alegoldstein/Webcam/Photos/home.png

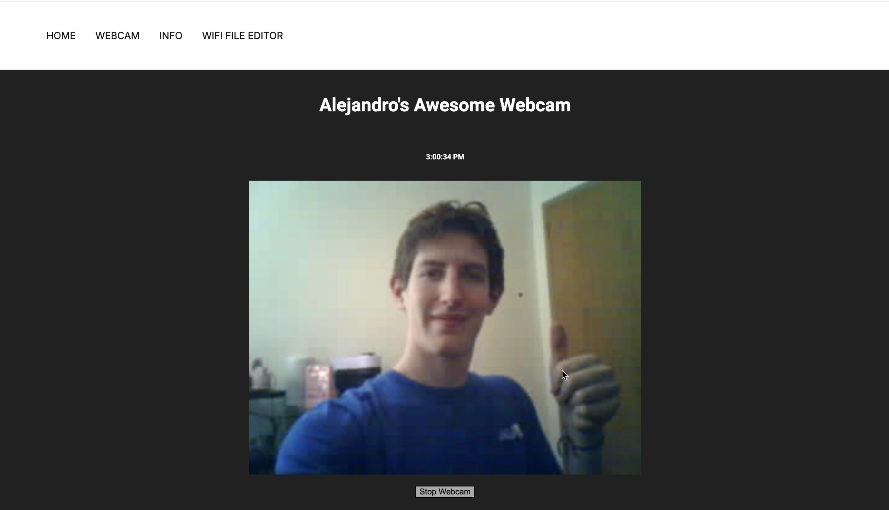
Photos/home.png
