alegoldstein/Webcam/EE326 Firmware/wifi.c

/*
 * wifi.c
 *
 * Created: 1/31/2023 1:02:43 PM
 *  Author: imikh
 */ 

#include <asf.h>
#include "wifi.h"

volatile uint32_t transfer_index = 0;
volatile uint32_t transfer_len = 0;

void SPI_Handler(void)
{
	uint32_t new_cmd = 0;
	static uint16_t data;
	uint8_t uc_pcs;

	if (spi_read_status(SPI) & SPI_SR_RDRF) {
		spi_read(SPI, &data, &uc_pcs);
		
		if (transfer_len--) {
			spi_write(SPI, transfer_index++, 0, 0);
		}
	}
}

void configure_usart_wifi(void)
{
	gpio_configure_pin(PIN_USART0_RXD_IDX, PIN_USART0_RXD_FLAGS);
	gpio_configure_pin(PIN_USART0_TXD_IDX, PIN_USART0_TXD_FLAGS);
	
	static uint32_t ul_sysclk;
	const sam_usart_opt_t wifi_usart_settings = {
		WIFI_USART_BAUDRATE,
		WIFI_USART_CHAR_LENGTH,
		WIFI_USART_PARITY,
		WIFI_USART_STOP_BITS,
		WIFI_USART_MODE,
		/* This field is only used in IrDA mode. */
		0
	};
	
	/* Get system clock. */
	ul_sysclk = sysclk_get_cpu_hz();
	
	pmc_enable_periph_clk(WIFI_USART_ID);
	
	usart_init_rs232(WIFI_USART,&wifi_usart_settings,ul_sysclk);

	/* Disable all the interrupts. */
	usart_disable_interrupt(WIFI_USART, ALL_INTERRUPT_MASK);
	
	/* Enable TX & RX function. */
	usart_enable_tx(WIFI_USART);
	usart_enable_rx(WIFI_USART);

	usart_enable_interrupt(WIFI_USART, US_IER_RXRDY);

	/* Configure and enable interrupt of USART. */
	NVIC_EnableIRQ(WIFI_USART_IRQn);
}

void configure_spi()
{
	gpio_configure_pin(SPI_MISO_GPIO, SPI_MISO_FLAGS);
	gpio_configure_pin(SPI_MOSI_GPIO, SPI_MOSI_FLAGS);
	gpio_configure_pin(SPI_SPCK_GPIO, SPI_SPCK_FLAGS);
	gpio_configure_pin(SPI_NPCS0_GPIO, SPI_NPCS0_FLAGS);
	
	/* Configure SPI interrupts for slave only. */
	NVIC_DisableIRQ(SPI_IRQn);
	NVIC_ClearPendingIRQ(SPI_IRQn);
	NVIC_SetPriority(SPI_IRQn, 0);
	NVIC_EnableIRQ(SPI_IRQn);
}

void spi_peripheral_initialize(void)
{
	spi_enable_clock(SPI);
	spi_disable(SPI);
	spi_reset(SPI);
	spi_set_slave_mode(SPI);
	spi_disable_mode_fault_detect(SPI);
	spi_set_peripheral_chip_select_value(SPI, SPI_CHIP_PCS);
	spi_set_clock_polarity(SPI, SPI_CHIP_SEL, SPI_CLK_POLARITY);
	spi_set_clock_phase(SPI, SPI_CHIP_SEL, SPI_CLK_PHASE);
	spi_set_bits_per_transfer(SPI, SPI_CHIP_SEL, SPI_CSR_BITS_8_BIT);
	spi_enable_interrupt(SPI, SPI_IER_RDRF);
	spi_enable(SPI);
}

void spi_prep_transfer(void)
{
	transfer_len = 100;
	transfer_index = 0;
}
