alegoldstein/Webcam/EE326 Firmware/ov7740_example.c

/**
 * \file
 *
 * \brief OV7740 image sensor capture example.
 *
 * Copyright (c) 2014-2018 Microchip Technology Inc. and its subsidiaries.
 *
 * \asf_license_start
 *
 * \page License
 *
 * Subject to your compliance with these terms, you may use Microchip
 * software and any derivatives exclusively with Microchip products.
 * It is your responsibility to comply with third party license terms applicable
 * to your use of third party software (including open source software) that
 * may accompany Microchip software.
 *
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
 * \asf_license_stop
 *
 */

/**
 * \mainpage OV7740 image sensor capture example.
 *
 * \section Purpose
 *
 * This example demonstrates how to configure the OV7740 to capture a picture
 * and display it on LCD.
 *
 * \section Requirements
 *
 * This package can be used with sam4s_wpir_rd board.
 *
 * \section Description
 *
 * This example first sets the PLLB to the system core clock and PLLA to clock
 * PCK0 (used to get data from image sensor). Next step is to configure the
 * LCD controller and display information to the user. Then external SRAM, which
 * is used to store data after acquisition, is configured. Finally this example
 * configures the OV7740 CMOS image sensor and the PIO capture.
 * When the user presses the push button, a picture is captured, stored
 * to the external SRAM memory and finally displayed on the LCD.
 *
 * \section Usage
 *
 * -# Build the program and download it inside the evaluation board.
 *
 */
/*
 * Support and FAQ: visit <a href="https://www.microchip.com/support/">Microchip Support</a>
 */

#include "asf.h"
#include "conf_board.h"
#include "conf_clock.h"

/* Uncomment this macro to work in black and white mode */
#define DEFAULT_MODE_COLORED

#ifndef PIO_PCMR_DSIZE_WORD
#  define PIO_PCMR_DSIZE_WORD PIO_PCMR_DSIZE(2)
#endif

/* TWI clock frequency in Hz (400KHz) */
#define TWI_CLK     (400000UL)

/* Pointer to the image data destination buffer */
uint8_t *//camera pin, variable, and function declarations
//camera TWI parameters



#ifndef camera_h
#define camera_h

#include "asf.h"
#include <stdint.h>
#include <stdio.h>
#include "pio.h"
//#include <twi_master.h>
#include <pmc.h>
#include <gpio.h>
#include <sysclk.h>
#include "ov2640.h"

extern volatile uint32_t image_len;

#define OV2640_DATA_BUS_PIO     PIOA
#define OV2640_DATA_BUS_ID      ID_PIOA
#define PIN_VSYNC_PIO           PIOA
#define OV2640_VSYNC_ID         ID_PIOA
#define OV2640_VSYNC_MASK       (1 << 15)
#define OV2640_VSYNC_TYPE       PIO_IT_RISE_EDGE
#define BOARD_TWI				TWI0

#define CAP_BUFFER_SIZE     (100000)         // 20KB, safe upper bound for JPEG 320x240
extern uint8_t g_p_uc_cap_dest_buf[];

//handler for rising edge of vsync, set flag
void vsync_handler(uint32_t ul_id, uint32_t ul_mask);

//configure vsync interrupt
void init_vsync_interrupts(void);

//configure TWI (two wire interface I2C)
void configure_twi(void);

//configure and initialize parallel capture 
void pio_capture_init(Pio *p_pio, uint32_t ul_id);

//use parallel capture and PDC to store images in buffer
uint8_t pio_capture_to_buffer(Pio *p_pio, uint8_t *uc_buf, uint32_t ul_size);

//configure camera pins and clk (XCLK), and call configure_twi()
void init_camera(void);

//configure camera registers
void configure_camera(void);

//capture image on rising edge of vsync, gets image length and returns 1 on success and 0 on fail
uint8_t start_capture(void);

//finds image length based on JPED protocol, can find start of image (SOI) before end of image (EOI)
//return 1 if success 0 and 0 if failure
uint8_t find_image_len(void);

#endif;

/* Rows size of capturing picture */
uint16_t g_us_cap_rows = IMAGE_HEIGHT;

/* Define display function and line size of captured picture according to the */
/* current mode (color or black and white) */
#ifdef DEFAULT_MODE_COLORED
	#define _display() draw_frame_yuv_color_int()

	/* (IMAGE_WIDTH *2 ) because ov7740 use YUV422 format in color mode */
	/* (draw_frame_yuv_color_int for more details) */
	uint16_t g_us_cap_line = (IMAGE_WIDTH * 2);
#else
	#define _display() draw_frame_yuv_bw8()

	uint16_t g_us_cap_line = (IMAGE_WIDTH);
#endif

/* Push button information (true if it's triggered and false otherwise) */
static volatile uint32_t g_ul_push_button_trigger = false;

/* Vsync signal information (true if it's triggered and false otherwise) */
static volatile uint32_t g_ul_vsync_flag = false;

/**
 * \brief Handler for vertical synchronisation using by the OV7740 image
 * sensor.
 */
static void vsync_handler(uint32_t ul_id, uint32_t ul_mask)
{
	unused(ul_id);
	unused(ul_mask);

	g_ul_vsync_flag = true;
}

/**
 * \brief Handler for button rising edge interrupt.
 */
static void button_handler(uint32_t ul_id, uint32_t ul_mask)
{
	unused(ul_id);
	unused(ul_mask);

	g_ul_push_button_trigger = true;
}

/**
 * \brief Intialize Vsync_Handler.
 */
static void init_vsync_interrupts(void)
{
	/* Initialize PIO interrupt handler, see PIO definition in conf_board.h
	**/
	pio_handler_set(OV7740_VSYNC_PIO, OV7740_VSYNC_ID, OV7740_VSYNC_MASK,
			OV7740_VSYNC_TYPE, vsync_handler);

	/* Enable PIO controller IRQs */
	NVIC_EnableIRQ((IRQn_Type)OV7740_VSYNC_ID);
}

/**
 * \brief Configure push button and initialize button_handler interrupt.
 */
static void configure_button(void)
{
	/* Configure PIO clock. */
	pmc_enable_periph_clk(PUSH_BUTTON_ID);

	/* Adjust PIO debounce filter using a 10 Hz filter. */
	pio_set_debounce_filter(PUSH_BUTTON_PIO, PUSH_BUTTON_PIN_MSK, 10);

	/* Initialize PIO interrupt handler, see PIO definition in conf_board.h
	**/
	pio_handler_set(PUSH_BUTTON_PIO, PUSH_BUTTON_ID, PUSH_BUTTON_PIN_MSK,
			PUSH_BUTTON_ATTR, button_handler);

	/* Enable PIO controller IRQs. */
	NVIC_EnableIRQ((IRQn_Type)PUSH_BUTTON_ID);

	/* Enable PIO interrupt lines. */
	pio_enable_interrupt(PUSH_BUTTON_PIO, PUSH_BUTTON_PIN_MSK);
}

/**
 * \brief Initialize PIO capture for the OV7740 image sensor communication.
 *
 * \param p_pio PIO instance to be configured in PIO capture mode.
 * \param ul_id Corresponding PIO ID.
 */
static void pio_capture_init(Pio *p_pio, uint32_t ul_id)
{
	/* Enable periphral clock */
	pmc_enable_periph_clk(ul_id);

	/* Disable pio capture */
	p_pio->PIO_PCMR &= ~((uint32_t)PIO_PCMR_PCEN);

	/* Disable rxbuff interrupt */
	p_pio->PIO_PCIDR |= PIO_PCIDR_RXBUFF;

	/* 32bit width*/
	p_pio->PIO_PCMR &= ~((uint32_t)PIO_PCMR_DSIZE_Msk);
	p_pio->PIO_PCMR |= PIO_PCMR_DSIZE_WORD;

	/* Only HSYNC and VSYNC enabled */
	p_pio->PIO_PCMR &= ~((uint32_t)PIO_PCMR_ALWYS);
	p_pio->PIO_PCMR &= ~((uint32_t)PIO_PCMR_HALFS);

#if !defined(DEFAULT_MODE_COLORED)
	/* Samples only data with even index */
	p_pio->PIO_PCMR |= PIO_PCMR_HALFS;
	p_pio->PIO_PCMR &= ~((uint32_t)PIO_PCMR_FRSTS);
#endif
}

/**
 * \brief Capture OV7740 data to a buffer.
 *
 * \param p_pio PIO instance which will capture data from OV7740 iamge sensor.
 * \param p_uc_buf Buffer address where captured data must be stored.
 * \param ul_size Data frame size.
 */
static uint8_t pio_capture_to_buffer(Pio *p_pio, uint8_t *uc_buf,
		uint32_t ul_size)
{
	/* Check if the first PDC bank is free */
	if ((p_pio->PIO_RCR == 0) && (p_pio->PIO_RNCR == 0)) {
		p_pio->PIO_RPR = (uint32_t)uc_buf;
		p_pio->PIO_RCR = ul_size;
		p_pio->PIO_PTCR = PIO_PTCR_RXTEN;
		return 1;
	} else if (p_pio->PIO_RNCR == 0) {
		p_pio->PIO_RNPR = (uint32_t)uc_buf;
		p_pio->PIO_RNCR = ul_size;
		return 1;
	} else {
		return 0;
	}
}

/**
 * \brief Intialize LCD display.
 */
static void display_init(void)
{
	struct ili9325_opt_t ili9325_display_opt;

	/* Enable peripheral clock */
	pmc_enable_periph_clk( ID_SMC );

	/* Configure SMC interface for LCD */
	smc_set_setup_timing(SMC, ILI9325_LCD_CS, SMC_SETUP_NWE_SETUP(2)
			| SMC_SETUP_NCS_WR_SETUP(2)
			| SMC_SETUP_NRD_SETUP(2)
			| SMC_SETUP_NCS_RD_SETUP(2));

	smc_set_pulse_timing(SMC, ILI9325_LCD_CS, SMC_PULSE_NWE_PULSE(4)
			| SMC_PULSE_NCS_WR_PULSE(4)
			| SMC_PULSE_NRD_PULSE(10)
			| SMC_PULSE_NCS_RD_PULSE(10));

	smc_set_cycle_timing(SMC, ILI9325_LCD_CS, SMC_CYCLE_NWE_CYCLE(10)
			| SMC_CYCLE_NRD_CYCLE(22));

	smc_set_mode(SMC, ILI9325_LCD_CS, SMC_MODE_READ_MODE
			| SMC_MODE_WRITE_MODE);

	/* Initialize display parameter */
	ili9325_display_opt.ul_width = ILI9325_LCD_WIDTH;
	ili9325_display_opt.ul_height = ILI9325_LCD_HEIGHT;
	ili9325_display_opt.foreground_color = COLOR_BLACK;
	ili9325_display_opt.background_color = COLOR_WHITE;

	/* Switch off backlight */
	aat31xx_disable_backlight();

	/* Initialize LCD */
	ili9325_init(&ili9325_display_opt);

	/* Set backlight level */
	aat31xx_set_backlight(AAT31XX_MAX_BACKLIGHT_LEVEL);

	/* Turn on LCD */
	ili9325_display_on();
}

/**
 * \brief Initialize PIO capture and the OV7740 image sensor.
 */
static void capture_init(void)
{
	twi_options_t opt;

	/* Init Vsync handler*/
	init_vsync_interrupts();

	/* Init PIO capture*/
	pio_capture_init(OV_DATA_BUS_PIO, OV_DATA_BUS_ID);

	/* Turn on ov7740 image sensor using power pin */
	ov_power(true, OV_POWER_PIO, OV_POWER_MASK);

	/* Init PCK0 to work at 24 Mhz */
	/* 96/4=24 Mhz */
	PMC->PMC_PCK[0] = (PMC_PCK_PRES_CLK_4 | PMC_PCK_CSS_PLLA_CLK);
	PMC->PMC_SCER = PMC_SCER_PCK0;
	while (!(PMC->PMC_SCSR & PMC_SCSR_PCK0)) {
	}

	/* Enable TWI peripheral */
	pmc_enable_periph_clk(ID_BOARD_TWI);

	/* Init TWI peripheral */
	opt.master_clk = sysclk_get_cpu_hz();
	opt.speed      = TWI_CLK;
	twi_master_init(BOARD_TWI, &opt);

	/* Configure TWI interrupts */
	NVIC_DisableIRQ(BOARD_TWI_IRQn);
	NVIC_ClearPendingIRQ(BOARD_TWI_IRQn);
	NVIC_SetPriority(BOARD_TWI_IRQn, 0);
	NVIC_EnableIRQ(BOARD_TWI_IRQn);

	/* ov7740 Initialization */
	while (ov_init(BOARD_TWI) == 1) {
	}

	/* ov7740 configuration */
	ov_configure(BOARD_TWI, QVGA_YUV422_20FPS);

	/* Wait 3 seconds to let the image sensor to adapt to environment */
	delay_ms(3000);
}

/**
 * \brief Start picture capture.
 */
static void start_capture(void)
{
	/* Set capturing destination address*/
	g_p_uc_cap_dest_buf = (uint8_t *)CAP_DEST;

	/* Set cap_rows value*/
	g_us_cap_rows = IMAGE_HEIGHT;

	/* Enable vsync interrupt*/
	pio_enable_interrupt(OV7740_VSYNC_PIO, OV7740_VSYNC_MASK);

	/* Capture acquisition will start on rising edge of Vsync signal.
	 * So wait g_vsync_flag = 1 before start process
	 */
	while (!g_ul_vsync_flag) {
	}

	/* Disable vsync interrupt*/
	pio_disable_interrupt(OV7740_VSYNC_PIO, OV7740_VSYNC_MASK);

	/* Enable pio capture*/
	pio_capture_enable(OV7740_DATA_BUS_PIO);

	/* Capture data and send it to external SRAM memory thanks to PDC
	 * feature */
	pio_capture_to_buffer(OV7740_DATA_BUS_PIO, g_p_uc_cap_dest_buf,
			(g_us_cap_line * g_us_cap_rows) >> 2);

	/* Wait end of capture*/
	while (!((OV7740_DATA_BUS_PIO->PIO_PCISR & PIO_PCIMR_RXBUFF) ==
			PIO_PCIMR_RXBUFF)) {
	}

	/* Disable pio capture*/
	pio_capture_disable(OV7740_DATA_BUS_PIO);

	/* Reset vsync flag*/
	g_ul_vsync_flag = false;
}

/**
 * \brief Configure SMC interface for SRAM.
 */
static void board_configure_sram( void )
{
	/* Enable peripheral clock */
	pmc_enable_periph_clk( ID_SMC );

	/* Configure SMC interface for SRAM */
	smc_set_setup_timing(SMC, SRAM_CS, SMC_SETUP_NWE_SETUP(2)
			| SMC_SETUP_NCS_WR_SETUP(0)
			| SMC_SETUP_NRD_SETUP(3)
			| SMC_SETUP_NCS_RD_SETUP(0));

	smc_set_pulse_timing(SMC, SRAM_CS, SMC_PULSE_NWE_PULSE(4)
			| SMC_PULSE_NCS_WR_PULSE(5)
			| SMC_PULSE_NRD_PULSE(4)
			| SMC_PULSE_NCS_RD_PULSE(6));

	smc_set_cycle_timing(SMC, SRAM_CS, SMC_CYCLE_NWE_CYCLE(6)
			| SMC_CYCLE_NRD_CYCLE(7));

	smc_set_mode(SMC, SRAM_CS, SMC_MODE_READ_MODE
			| SMC_MODE_WRITE_MODE);
}

#ifdef DEFAULT_MODE_COLORED

/**
 * \brief Take a 32 bit variable in parameters and returns a value between 0 and
 * 255.
 *
 * \param i Enter value .
 * \return i if 0<i<255, 0 if i<0 and 255 if i>255
 */
static inline uint8_t clip32_to_8( int32_t i )
{
	if (i > 255) {
		return 255;
	}

	if (i < 0) {
		return 0;
	}

	return (uint8_t)i;
}

/**
 * \brief Draw LCD in color with integral algorithm.
 */
static void draw_frame_yuv_color_int( void )
{
	uint32_t ul_cursor;
	int32_t l_y1;
	int32_t l_y2;
	int32_t l_v;
	int32_t l_u;
	int32_t l_blue;
	int32_t l_green;
	int32_t l_red;
	uint8_t *p_uc_data;

	p_uc_data = (uint8_t *)g_p_uc_cap_dest_buf;

	/* Configure LCD to draw captured picture */
	LCD_IR(0);
	LCD_IR(ILI9325_ENTRY_MODE);
	LCD_WD(((ILI9325_ENTRY_MODE_BGR | ILI9325_ENTRY_MODE_AM |
			ILI9325_ENTRY_MODE_DFM | ILI9325_ENTRY_MODE_TRI |
			ILI9325_ENTRY_MODE_ORG) >> 8) & 0xFF);
	LCD_WD((ILI9325_ENTRY_MODE_BGR | ILI9325_ENTRY_MODE_AM |
			ILI9325_ENTRY_MODE_DFM | ILI9325_ENTRY_MODE_TRI |
			ILI9325_ENTRY_MODE_ORG) & 0xFF);
	ili9325_draw_prepare(0, 0, IMAGE_HEIGHT, IMAGE_WIDTH);

	/* OV7740 Color format is YUV422. In this format pixel has 4 bytes
	 * length (Y1,U,Y2,V).
	 * To display it on LCD,these pixel need to be converted in RGB format.
	 * The output of this conversion is two 3 bytes pixels in (B,G,R)
	 * format. First one is calculed using Y1,U,V and the other one with
	 * Y2,U,V. For that reason cap_line is twice bigger in color mode
	 * than in black and white mode. */
	for (ul_cursor = IMAGE_WIDTH * IMAGE_HEIGHT; ul_cursor != 0;
			ul_cursor -= 2, p_uc_data += 4) {
		l_y1 = p_uc_data[0]; /* Y1 */
		l_y1 -= 16;
		l_v = p_uc_data[3]; /* V */
		l_v -= 128;
		l_u = p_uc_data[1]; /* U */
		l_u -= 128;

		l_blue = 516 * l_v + 128;
		l_green = -100 * l_v - 208 * l_u + 128;
		l_red = 409 * l_u + 128;

		/* BLUE */
		LCD_WD( clip32_to_8((298 * l_y1 + l_blue) >> 8));
		/* GREEN */
		LCD_WD( clip32_to_8((298 * l_y1 + l_green) >> 8));
		/* RED */
		LCD_WD( clip32_to_8((298 * l_y1 + l_red) >> 8));

		l_y2 = p_uc_data[2]; /* Y2 */
		l_y2 -= 16;
		LCD_WD( clip32_to_8((298 * l_y2 + l_blue) >> 8));
		LCD_WD( clip32_to_8((298 * l_y2 + l_green) >> 8));
		LCD_WD( clip32_to_8((298 * l_y2 + l_red) >> 8));
	}
}

#else

/**
 * \brief Draw LCD in black and white with integral algorithm.
 */
static void draw_frame_yuv_bw8( void )
{
	volatile uint32_t ul_cursor;
	uint8_t *p_uc_data;

	p_uc_data = (uint8_t *)g_p_uc_cap_dest_buf;

	/* Configure LCD to draw captured picture */
	LCD_IR(0);
	LCD_IR(ILI9325_ENTRY_MODE);
	LCD_WD(((ILI9325_ENTRY_MODE_BGR | ILI9325_ENTRY_MODE_AM |
			ILI9325_ENTRY_MODE_DFM | ILI9325_ENTRY_MODE_TRI |
			ILI9325_ENTRY_MODE_ORG) >> 8) & 0xFF);
	LCD_WD((ILI9325_ENTRY_MODE_BGR | ILI9325_ENTRY_MODE_AM |
			ILI9325_ENTRY_MODE_DFM | ILI9325_ENTRY_MODE_TRI |
			ILI9325_ENTRY_MODE_ORG) & 0xFF);
	ili9325_draw_prepare(0, 0, IMAGE_HEIGHT, IMAGE_WIDTH);

	/* LCD pixel has 24bit data. In black and White mode data has 8bit only
	 * so
	 * this data must be written three time in LCD memory.
	 */
	for (ul_cursor = IMAGE_WIDTH * IMAGE_HEIGHT; ul_cursor != 0;
			ul_cursor--, p_uc_data++) {
		/* Black and White using Y */
		LCD_WD( *p_uc_data );
		LCD_WD( *p_uc_data );
		LCD_WD( *p_uc_data );
	}
}

#endif

/**
 * \brief Application entry point for image sensor capture example.
 *
 * \return Unused (ANSI-C compatibility).
 */
int main(void)
{
	sysclk_init();
	board_init();

	/* OV7740 send image sensor data at 24 Mhz. For best performances, PCK0
	 * which will capture OV7740 data, has to work at 24Mhz. It's easier and
	 * optimum to use one PLL for core (PLLB) and one other for PCK0 (PLLA).
	 */
	pmc_enable_pllack(7, 0x1, 1); /* PLLA work at 96 Mhz */

	/* LCD display initialization */
	display_init();

	/* LCD display information */
	ili9325_fill(COLOR_TURQUOISE);
	ili9325_draw_string(0, 20,
			(uint8_t *)"OV7740 image sensor\ncapture example");
	ili9325_draw_string(0, 80,
			(uint8_t *)"Please Wait during \ninitialization");

	/* Configure SMC interface for external SRAM. This SRAM will be used
	 * to store picture during image sensor acquisition.
	 */
	board_configure_sram();

	/* Configure push button to generate interrupt when the user press it */
	configure_button();

	/* OV7740 image sensor initialization*/
	capture_init();

	/* LCD display information*/
	ili9325_fill(COLOR_TURQUOISE);
	ili9325_draw_string(0, 20,
			(uint8_t *)"OV7740 image sensor\ncapture example");
	ili9325_draw_string(0, 80,
			(uint8_t *)"Please Press button\nto take and display\na picture");

	while (1) {
		while (!g_ul_push_button_trigger) { /* Press push button to get
			                             * out */
		}
		/* Reset push button trigger flag */
		g_ul_push_button_trigger = false;

		/* Capture a picture and send corresponding data to external
		 * memory */
		start_capture();

		/* Load picture data from external memory and display it on the
		 * LCD */
		_display();
	}
}
